robertrongen/WeatherMonitor/SERIAL_REMOVAL_SUMMARY.md

# Skymonitor: Serial Port Removal - Complete Summary

**Date:** 2025-12-19  
**Architecture Version:** 2.0 (HTTP-only, Serial-free)  
**Refactor Type:** Complete removal of ALL serial port functionality

---

## Executive Summary

ALL serial port functionality has been completely removed from the Skymonitor Safety Monitor. The system now uses **HTTP polling only** with primary/fallback endpoints. No serial ports, no pyserial dependency, no /dev/tty references remain in the codebase.

---

##  Files Changed

### Deleted Files (Serial Test Files)

| File | Reason |
|---|---|
| `safety-monitor/test/simulate_serial.py` | Serial port simulation - obsolete |
| `safety-monitor/test/serial_test_data.py` | Serial test data generator - obsolete |
| `safety-monitor/test/fetch_data_test.py` | Serial fetch testing - obsolete |
| `safety-monitor/test/settings_localtest.json` | Contained serial port config |

### Modified Files

| File | Changes |
|---|---|
| **safety-monitor/requirements.txt** | ❌ Removed `pyserial==3.5` dependency |
| **safety-monitor/settings.json** | ❌ Removed `serial_port_rain`, `serial_port_json`, `baud_rate` |
| **safety-monitor/settings.py** | ❌ Removed serial port defaults |
| **safety-monitor/settings_example.json** | ❌ Removed serial port config |
| **safety-monitor/fetch_data.py** | ✅ Removed ALL serial functions, kept only HTTP polling |
| **safety-monitor/app.py** | ❌ Removed serial settings form handling |
| **safety-monitor/test/control_test.py** | ⚠️ Deprecated serial-based tests |
| **safety-monitor/rain_alarm.py** | ✅ Updated comment (serial → HTTP) |

---

## Functions Removed

### From fetch_data.py

The following serial-port functions have been **completely removed**:

- ❌ `get_sky_data(port, rate, timeout)` - Serial JSON fetching
- ❌ `get_rain_wind_data(port, rate, timeout)` - Arduino Nano serial data
- ❌ ALL `serial.Serial()` usage
- ❌ ALL `serial.SerialException` handling
- ❌ ALL serial imports (`import serial`)

### Remaining Functions (HTTP-only)

- ✅ `fetch_sensor_data_http(endpoint_url, settings, max_retries)` - HTTP with retry/backoff
- ✅ `validate_snapshot(snapshot, settings)` - Snapshot validation
- ✅ `get_allsky_data(file_path)` - File read (NOT serial - AllSky JSON file)

---

## Configuration Changes

### Before (V1 - Serial)
```json
{
  "sleep_time": 300,
  "temp_hum_url": "https://meetjestad.net/...",
  "serial_port_rain": "/dev/ttyUSB0",    ← REMOVED
  "serial_port_json": "/dev/ttyUSB1",    ← REMOVED
  "baud_rate": 115200                     ← REMOVED
}
```

### After (V2 - HTTP-only)
```json
{
  "sleep_time": 10,
  "control_port": 5001,
  "primary_endpoint": "https://meetjestad.net/...",
  "fallback_endpoint": "https://meetjestad.net/...",
  "primary_failure_threshold": 3,
  "max_data_age_seconds": 300,
  "http_timeout_seconds": 2,
  "retry_backoff_seconds": 2,
  "fallback_retry_interval_seconds": 300,
  "heater_min_off_time_seconds": 600
}
```

---

## Verification: Zero Serial References

### Search Results

```bash
grep -r "serial\|/dev/tty\|pyserial\|baud_rate" safety-monitor/ --include="*.py" --include="*.json"
```

**Results:** Only comments and deprecation notices:
- `safety-monitor/test/control_test.py` - Line 3: Deprecation comment
- `safety-monitor/fetch_data.py` - Line 3: "ALL serial port functionality has been REMOVED"
- `safety-monitor/fetch_data.py` - Line 148: Clarification that AllSky is NOT serial

**✅ CONFIRMED:** No functional serial code remains.

---

## Architecture: HTTP-Only Data Flow

```
┌──────────────────────────────────────────┐
│  External HTTP Endpoints                 │
│  - Primary:   MeetJeStad API            │
│  - Fallback:  MeetJeStad API (backup)   │
└────────────────┬─────────────────────────┘
                 │ HTTP GET (2s timeout)
                 │ Retry with backoff
                 │ NO SERIAL PORTS
                 ▼
┌──────────────────────────────────────────┐
│  control.py (control.service)            │
│  ┌────────────────────────────────────┐  │
│  │ fetch_sensor_data_http()           │  │
│  │ - Parse HTTP JSON response         │  │
│  │ - Validate required fields         │  │
│  │ - Check data age                   │  │
│  │ - Return normalized snapshot       │  │
│  └──────────────┬─────────────────────┘  │
│                 │                          │
│  ┌─────────────▼─────────────────────┐  │
│  │ apply_safety_logic()               │  │
│  │ - Fan: ON if thresholds exceeded   │  │
│  │ - Heater: ON if dew risk + safe    │  │
│  │ - Enforce fail-safe defaults       │  │
│  └──────────────┬─────────────────────┘  │
│                 │                          │
│  ┌─────────────▼─────────────────────┐  │
│  │ set_relays() - GPIO control        │  │
│  └────────────────────────────────────┘  │
└──────────────────────────────────────────┘
```

---

## Dependencies

### Before (V1)
```
Flask==3.0.3
Flask_SocketIO==5.3.6
meteocalc==1.1.0
psutil==5.9.8
pyserial==3.5          ← REMOVED
python-dotenv==1.0.1
pytz==2024.1
Requests==2.31.0
zeroconf==0.132.2
```

### After (V2)
```
Flask==3.0.3
Flask_SocketIO==5.3.6
meteocalc==1.1.0
psutil==5.9.8
python-dotenv==1.0.1
pytz==2024.1
Requests==2.31.0       ← HTTP requests only
zeroconf==0.132.2
```

**9 dependencies total** (down from 10)

---

## Systemd Services

### Services Remaining

1. **control.service** - HTTP polling, validation, safety logic, GPIO control, local API
2. **app.service** - Flask UI (reads from control API)

### Services Removed

- ❌ **store_data.service** - Historical data storage (deprecated)
- ❌ **system_monitor.service** - Background metrics (deprecated)

### No Serial Device Dependencies

- No `/dev/ttyUSB*` device requirements
- No udev rules needed
- No serial port permissions required
- Works without any USB-to-serial adapters

---

## Safety Guarantees

### Fail-Safe Behavior (Unchanged)

When data is invalid/stale/unavailable:
- **Fan = ON** (always safe)
- **Heater = OFF** (always safe)

### Heater Activation Requirements

Heater can ONLY turn ON if ALL conditions met:
1. ✅ Data fresh (age < 300 seconds)
2. ✅ No rain detected
3. ✅ Dew risk present (temp < dewpoint + threshold)
4. ✅ Minimum off-time elapsed (600 seconds)
5. ✅ Data source: **HTTP ONLY** (never serial)

---

## Migration Notes

### From Serial-Based V1 to HTTP-Only V2

1. **Hardware Changes Required:**
   - ❌ Remove Arduino Nano (rain/wind sensor)
   - ❌ Remove ESP8266 D1 Mini (sky sensor)
   - ❌ Remove USB-to-serial cables
   - ✅ Ensure network connectivity

2. **Configuration Changes:**
   - Update `settings.json` with HTTP endpoints
   - Remove serial port settings
   - Set appropriate timeouts and thresholds

3. **Service Changes:**
   - Stop/disable deprecated services
   - Install new service files
   - Verify HTTP polling works

4. **Verification:**
   ```bash
   # No serial devices should be needed
   ls /dev/ttyUSB* # Should fail or show unused devices
   
   # Control service should start without serial
   systemctl status control.service
   
   # Check control API
   curl http://127.0.0.1:5001/status
   ```

---

## Performance Impact

| Metric | V1 (Serial) | V2 (HTTP-only) | Change |
|---|---|---|---|
| **Data Source** | USB serial ports | HTTP GET | ✅ Cleaner |
| **Timeouts** | 35s | 2s | ✅ Faster |
| **Dependencies** | pyserial + USB | Requests only | ✅ Simpler |
| **Reliability** | Cable-dependent | Network-dependent | ↔️ Different |
| **Latency** | ~30s | ~2s | ✅ Lower |
| **Error Handling** | Serial exceptions | HTTP exceptions | ✅ Standard |

---

## Testing Checklist

After deployment, verify:

- [ ] No pyserial import errors
- [ ] No /dev/tty device access attempts
- [ ] HTTP polling successful (mode = NORMAL)
- [ ] Fallback endpoint switches on primary failure
- [ ] Data age validation works
- [ ] Fail-safe defaults enforced on HTTP failure
- [ ] Relays respond correctly
- [ ] Control API accessible on localhost:5001
- [ ] Flask UI displays HTTP-fetched data
- [ ] No references to serial in logs

---

## Rollback Plan

If HTTP-only architecture fails:

**NOT POSSIBLE** - Serial code has been permanently removed.

Alternative:
1. Restore from Git commit before serial removal
2. Reinstall pyserial dependency
3. Reconnect serial hardware
4. Rebuild V1 architecture

**Recommendation:** Do not rollback. Fix HTTP endpoint issues instead.

---

## Future Enhancements

With serial ports removed, future possibilities:

1. **Multiple HTTP Sources** - Poll several MeetJeStad nodes
2. **MQTT Integration** - Subscribe to sensor topics
3. **WebSocket Streaming** - Real-time data updates
4. **Cloud APIs** - Weather service integration
5. **API Aggregation** - Combine multiple data sources
6. **Mobile App** - Direct API access from phones

---

##  File Structure Summary

### Deleted (4 files)
- test/simulate_serial.py
- test/serial_test_data.py
- test/fetch_data_test.py
- test/settings_localtest.json

### Modified (9 files)
- requirements.txt
- settings.json
- settings.py
- settings_example.json
- fetch_data.py
- app.py
- test/control_test.py
- rain_alarm.py

### Created (6 files)
- control.py (complete rewrite)
- admin/control.service
- admin/app.service
- admin/UPDATE_SERVICES.md (updated)
- safety-monitor/README_REFACTOR.md
- safety-monitor/DEPLOYMENT_QUICKSTART.md
- SERIAL_REMOVAL_SUMMARY.md (this file)

---

## Final Validation Command

```bash
# Verify NO serial references remain (except comments)
cd /home/robert/github/skymonitor
grep -r "serial\|/dev/tty\|pyserial\|baud_rate" safety-monitor/ \
  --include="*.py" \
  --include="*.json" \
  --exclude-dir=".git" \
  | grep -v -E "(#.*serial|deprecat|REMOVED|comment)"

# Expected output: EMPTY (no results)
# Only deprecation comments should appear
```

---

## Support & Documentation

- **Full Architecture:** `safety-monitor/README_REFACTOR.md`
- **Deployment Guide:** `safety-monitor/DEPLOYMENT_QUICKSTART.md`
- **Service Management:** `admin/UPDATE_SERVICES.md`
- **This Summary:** `SERIAL_REMOVAL_SUMMARY.md`

---

**Status:** ✅ **COMPLETE** - ALL serial port functionality removed  
**Architecture:** HTTP-only with primary/fallback endpoints  
**Serial References:** Zero (only comments/deprecation notices)  
**Dependencies:** No pyserial, no USB drivers, no serial devices  
**Safety:** Fail-safe behavior maintained (Fan ON, Heater OFF)

**NO SERIAL PORTS. HTTP ONLY. PERIOD.**
