robertrongen/WeatherMonitor/safety-monitor/app_logging.py

# app_logging.py
import logging
import logging.handlers
import os
import sys
from dotenv import load_dotenv
import smtplib
from email.mime.text import MIMEText
import socket
import time
from datetime import datetime, timedelta

load_dotenv()

# Track last log times for messages
last_logged_time = {}
log_interval = timedelta(minutes=1)  # Default log interval

def should_log(message, interval=log_interval):
    """
    Determines if a log message should be logged based on the interval.
    Avoids duplicate log entries within the specified interval.
    """
    current_time = datetime.now()
    if message in last_logged_time and current_time - last_logged_time[message] < interval:
        return False
    last_logged_time[message] = current_time
    return True

def setup_handlers(logger, log_file, log_level=logging.ERROR, to_stdout=True):
    log_directory = "/home/robert/WeatherMonitor/logs"
    if not os.path.exists(log_directory):
        os.makedirs(log_directory)
    log_file_path = os.path.join(log_directory, log_file)

    if not any(isinstance(h, logging.handlers.RotatingFileHandler) for h in logger.handlers):
        file_handler = logging.handlers.RotatingFileHandler(log_file_path, maxBytes=1048576, backupCount=5)
        file_formatter = logging.Formatter('%(asctime)s - %(name)s - %(levelname)s - %(message)s')
        file_handler.setFormatter(file_formatter)
        logger.addHandler(file_handler)

    logger.setLevel(log_level)

    if to_stdout:
        if not any(isinstance(h, logging.StreamHandler) for h in logger.handlers):
            console_handler = logging.StreamHandler(sys.stdout)
            console_formatter = logging.Formatter('%(asctime)s - %(name)s - %(levelname)s - %(message)s')
            console_handler.setFormatter(console_formatter)
            logger.addHandler(console_handler)

def setup_email_logging(logger, attempt_to_email_errors=True):
    # Add specific conditions for logging
    # class AlertFilter(logging.Filter):
    #     def filter(self, record):
    #         return "High CPU temperature" in record.getMessage() or "High disk usage" in record.getMessage()
    email_host = os.getenv('EMAIL_HOST')
    email_port = int(os.getenv('EMAIL_PORT'))
    email_username = os.getenv('EMAIL_USERNAME')
    email_password = os.getenv('EMAIL_PASSWORD')

    # Email error logger setup
    email_error_logger = logging.getLogger('email_error')
    if not email_error_logger.handlers:
        fh = logging.FileHandler('email_errors.log')
        fh.setLevel(logging.ERROR)
        formatter = logging.Formatter('%(asctime)s - %(levelname)s - %(message)s')
        fh.setFormatter(formatter)
        email_error_logger.addHandler(fh)

    resolved = False
    for _ in range(3):  # Try to resolve up to 3 times
        try:
            socket.gethostbyname(email_host)
            resolved = True
            break
        except socket.gaierror as e:
            email_error_logger.error("DNS resolution failed for %s. Retrying...", email_host)
            time.sleep(5)  # Wait for 5 seconds before retrying

    if not resolved:
        email_error_logger.error("Failed to resolve SMTP server address after multiple attempts.")
        return

    try:
        server = smtplib.SMTP(email_host, email_port)
        server.starttls()  # Secure the connection
        server.login(email_username, email_password)
        server.quit()

        mail_handler = logging.handlers.SMTPHandler(
            mailhost=(email_host, email_port),
            fromaddr=email_username,
            toaddrs="rongen.robert@gmail.com",
            subject="Critical Error Logged",
            credentials=(email_username, email_password),
            secure=()
        )
        mail_handler.setLevel(logging.ERROR)
        mail_handler.setFormatter(logging.Formatter('%(asctime)s - %(name)s - %(levelname)s - %(message)s'))
        logger.addHandler(mail_handler)
    except Exception as e:
        email_error_logger.error("Failed to set up email logging: %s", str(e))


def setup_logger(name, log_file, level=logging.INFO):
    try:
        logger = logging.getLogger(name)
        setup_handlers(logger, log_file, log_level=level)  # Setup with console output
        if os.getenv("ENABLE_EMAIL_LOGGING") == "1":
            setup_email_logging(logger)
        return logger
    except Exception as e:
        sys.stderr.write("Failed to set up logger: {}\n".format(e))
        sys.exit(1)
