robertrongen/WeatherMonitor/firmware/display-client/secrets.h

// secrets.h
#ifndef SECRETS_H
#define SECRETS_H

#define STASSID1 "Wodan"           // Wifi SSID 1 (case sensitive)
#define STAPSK1  "u$UpB22&"        // WiFi password 1
#define STASSID2 "Betelgeuze"
#define STAPSK2  "AnnSan4281"
#define STASSID3 "Orion"
#define STAPSK3  "smartys!!"
#define STASSID4 "reserve"
#define STAPSK4  "reserve"

#endif // SECRETS_H
