robertrongen/WeatherMonitor/safety-monitor/test/control_test.py

# control_test.py
# === DEPRECATED ===
# This test file is deprecated as it tests the old serial-based architecture.
# The new HTTP-only architecture requires different testing approach.
# TODO: Create new tests for HTTP polling, fallback logic, and API endpoints
# ===================

import unittest
from unittest.mock import patch
from math import log10
from weather_indicators import calculate_indicators

class TestWeatherIndicators(unittest.TestCase):
    """Tests for weather indicator calculations (still valid)"""
    
    def test_calculate_indicators(self):
        # Example input data
        ambient_temperature = 20.0  # degrees Celsius
        sky_temperature = 15.0  # degrees Celsius
        sqm_lux = 200.0  # arbitrary lux value

        # Expected outputs calculated manually or with known good data
        expected_cloud_coverage = (sky_temperature - ambient_temperature) / ambient_temperature
        expected_cloud_coverage_indicator = ambient_temperature - sky_temperature
        expected_brightness = 22.0 - 2.512 * log10(sqm_lux)
        expected_bortle = 1539.7 * 2.7 ** (-0.28 * expected_brightness)

        # Execute the function with test data
        cloud_coverage, cloud_coverage_indicator, brightness, bortle = calculate_indicators(
            ambient_temperature, sky_temperature, sqm_lux)

        # Assert that returned values match expected values with detailed messages
        self.assertAlmostEqual(cloud_coverage, expected_cloud_coverage, places=5,
            msg=f"Test for Cloud Coverage Failed: Expected {expected_cloud_coverage}, Got {cloud_coverage}")
        self.assertAlmostEqual(cloud_coverage_indicator, expected_cloud_coverage_indicator, places=5,
            msg=f"Test for Cloud Coverage Indicator Failed: Expected {expected_cloud_coverage_indicator}, Got {cloud_coverage_indicator}")
        self.assertAlmostEqual(brightness, expected_brightness, places=5,
            msg=f"Test for Brightness Failed: Expected {expected_brightness}, Got {brightness}")
        self.assertAlmostEqual(bortle, expected_bortle, places=5,
            msg=f"Test for Bortle Failed: Expected {expected_bortle}, Got {bortle}")

if __name__ == '__main__':
    print("WARNING: Serial-based control tests removed. Only weather indicator tests remain.")
    print("TODO: Create new tests for HTTP-only architecture")
    unittest.main()
